Maitneel/JoySmall20/firmwere_srcs/JoySmall20/define_custom_keymap.ino

#include <avr/pgmspace.h> 
#include "Layer.h"
#include "define_custom_size.h"

const struct LayoutSet layout_set PROGMEM = {
    NUMBER_OF_LAYER_SET,
    {
        {
            2, // number_of_layer
            { // layer_key
                {0, 0, 0, 0, 0},
                {0, 0, 0, 0, 0},
                {0, 0, 0, 0, 0},
                {1, 0, 0, 0, 0},
            },
            { // layer
                { // layer[0]
                    {
                        {UNDEFINED_KEY, UNDEFINED_KEY, UNDEFINED_KEY, UNDEFINED_KEY, UNDEFINED_KEY},
                        {UNDEFINED_KEY, UNDEFINED_KEY, UNDEFINED_KEY, UNDEFINED_KEY, UNDEFINED_KEY},
                        {UNDEFINED_KEY, UNDEFINED_KEY, UNDEFINED_KEY, UNDEFINED_KEY, UNDEFINED_KEY},
                        {UNDEFINED_KEY, UNDEFINED_KEY, UNDEFINED_KEY, UNDEFINED_KEY, UNDEFINED_KEY},
                    },
                    {
                        {'a', 'a', 'a', 'a', 'a'},
                        {'b', 'b', 'b', 'b', 'b'},
                        {'c', 'c', 'c', 'c', 'c'},
                        {'d', 'd', 'd', 'd', 'd'}
                    },
                    {false, 'J', UNDEFINED_KEY},
                    UNDEFINED_KEY,
                    'R',
                },
                {
                    { // layer[1]
                        {UNDEFINED_KEY, UNDEFINED_KEY, UNDEFINED_KEY, UNDEFINED_KEY, UNDEFINED_KEY},
                        {UNDEFINED_KEY, UNDEFINED_KEY, UNDEFINED_KEY, UNDEFINED_KEY, UNDEFINED_KEY},
                        {UNDEFINED_KEY, UNDEFINED_KEY, UNDEFINED_KEY, UNDEFINED_KEY, UNDEFINED_KEY},
                        {UNDEFINED_KEY, UNDEFINED_KEY, UNDEFINED_KEY, UNDEFINED_KEY, UNDEFINED_KEY},
                    },
                    {
                        {'e', 'e', 'e', 'e', 'e'},
                        {'f', 'f', 'f', 'f', 'f'},
                        {'g', 'g', 'g', 'g', 'g'},
                        {'h', 'h', 'h', 'h', 'h'}
                    },
                    {true, 'J', UNDEFINED_KEY},
                    UNDEFINED_KEY,
                    'R',
                }
            }
        },
        {
            2, // number_of_layer
            { // layer_key
                {0, 0, 0, 0, 0},
                {0, 0, 0, 0, 0},
                {0, 0, 0, 0, 0},
                {1, 0, 0, 0, 0},
            },
            { // layer
                { // layer[0]
                    {
                        {UNDEFINED_KEY, UNDEFINED_KEY, UNDEFINED_KEY, UNDEFINED_KEY, UNDEFINED_KEY},
                        {UNDEFINED_KEY, UNDEFINED_KEY, UNDEFINED_KEY, UNDEFINED_KEY, UNDEFINED_KEY},
                        {UNDEFINED_KEY, UNDEFINED_KEY, UNDEFINED_KEY, UNDEFINED_KEY, UNDEFINED_KEY},
                        {UNDEFINED_KEY, UNDEFINED_KEY, UNDEFINED_KEY, UNDEFINED_KEY, UNDEFINED_KEY},
                    },
                    {
                        {'i', 'i', 'i', 'i', 'i'},
                        {'j', 'j', 'j', 'j', 'j'},
                        {'k', 'k', 'k', 'k', 'k'},
                        {'l', 'l', 'l', 'l', 'l'}
                    },
                    {false, 'J', UNDEFINED_KEY},
                    UNDEFINED_KEY,
                    'R',
                },
                {
                    { // layer[1]
                        {UNDEFINED_KEY, UNDEFINED_KEY, UNDEFINED_KEY, UNDEFINED_KEY, UNDEFINED_KEY},
                        {UNDEFINED_KEY, UNDEFINED_KEY, UNDEFINED_KEY, UNDEFINED_KEY, UNDEFINED_KEY},
                        {UNDEFINED_KEY, UNDEFINED_KEY, UNDEFINED_KEY, UNDEFINED_KEY, UNDEFINED_KEY},
                        {UNDEFINED_KEY, UNDEFINED_KEY, UNDEFINED_KEY, UNDEFINED_KEY, UNDEFINED_KEY},
                    },
                    {
                        {'m', 'm', 'm', 'm', 'm'},
                        {'n', 'n', 'n', 'n', 'n'},
                        {'o', 'o', 'o', 'o', 'o'},
                        {'p', 'p', 'p', 'p', 'p'}
                    },
                    {false, 'J', UNDEFINED_KEY},
                    UNDEFINED_KEY,
                    'R',
                }
            }
        },
        {
            2, // number_of_layer
            { // layer_key
                {0, 0, 0, 0, 0},
                {0, 0, 0, 0, 0},
                {0, 0, 0, 0, 0},
                {1, 0, 0, 0, 0},
            },
            { // layer
                { // layer[0]
                    {
                        {UNDEFINED_KEY, UNDEFINED_KEY, UNDEFINED_KEY, UNDEFINED_KEY, UNDEFINED_KEY},
                        {UNDEFINED_KEY, UNDEFINED_KEY, UNDEFINED_KEY, UNDEFINED_KEY, UNDEFINED_KEY},
                        {UNDEFINED_KEY, UNDEFINED_KEY, UNDEFINED_KEY, UNDEFINED_KEY, UNDEFINED_KEY},
                        {UNDEFINED_KEY, UNDEFINED_KEY, UNDEFINED_KEY, UNDEFINED_KEY, UNDEFINED_KEY},
                    },
                    {
                        {'r', 'r', 'r', 'r', 'r'},
                        {'s', 's', 's', 's', 's'},
                        {'t', 't', 't', 't', 't'},
                        {'u', 'u', 'u', 'u', 'u'}
                    },
                    {false, 'J', UNDEFINED_KEY},
                    UNDEFINED_KEY,
                    'R',
                },
                {
                    { // layer[1]
                        {UNDEFINED_KEY, UNDEFINED_KEY, UNDEFINED_KEY, UNDEFINED_KEY, UNDEFINED_KEY},
                        {UNDEFINED_KEY, UNDEFINED_KEY, UNDEFINED_KEY, UNDEFINED_KEY, UNDEFINED_KEY},
                        {UNDEFINED_KEY, UNDEFINED_KEY, UNDEFINED_KEY, UNDEFINED_KEY, UNDEFINED_KEY},
                        {UNDEFINED_KEY, UNDEFINED_KEY, UNDEFINED_KEY, UNDEFINED_KEY, UNDEFINED_KEY},
                    },
                    {
                        {'v', 'v', 'v', 'v', 'v'},
                        {'w', 'w', 'w', 'w', 'w'},
                        {'x', 'x', 'x', 'x', 'x'},
                        {'y', 'y', 'y', 'y', 'y'}
                    },
                    {false, 'J', UNDEFINED_KEY},
                    UNDEFINED_KEY,
                    'R',
                }
            }
        }
    }
};
