Maitneel/JoySmall20/firmwere_srcs/JoySmall20/Layer.h

#ifndef INCLUDE_LAYER_H_
#define INCLUDE_LAYER_H_

#include "define_custom_size.h"

#define LAYER_HEIGHT 4
#define LAYER_WIDTH 5

#define UNDEFINED_KEY 0

struct Joystick {
    bool is_wheel;
    unsigned char switch_key; 
    unsigned char switch_mouse;
};

struct Layer {
    unsigned char mousemap[LAYER_HEIGHT][LAYER_WIDTH];
    unsigned char keymap[LAYER_HEIGHT][LAYER_WIDTH];
    Joystick joy;
    unsigned char re_mouse;
    unsigned char re_key;
};


struct Layout {
    uint8_t number_of_layer;
    uint8_t layer_key[LAYER_HEIGHT][LAYER_WIDTH];
    struct Layer layer[NUMBER_OF_LAYER];
};

struct LayoutSet {
    const uint8_t number_of_layer;
    const Layout layout[NUMBER_OF_LAYER_SET];
};


#endif // INCLUDE_LAYER_H_
