Maitneel/JoySmall20/firmwere_srcs/JoySmall20/debug.h

#ifndef INCLUDE_DEBUG_H_
#define INCLUDE_DEBUG_H_

#include "Layer.h"

void debug_char(const char *str, const char c);
void debug_int(const char *str, const int n);
void debug_ptr(const char *str, void *ptr);
void print_layer(const struct Layer *layer);
void print_layout(struct Layout *layout);


#endif // INCLUDE_DEBUG_H_
